nickbild/zapper_phone/transmitter_schematic/transmitter/transmitter.kicad_sch

## KiCad design transmitter_schematic/transmitter/transmitter.kicad_sch (2025-05-16)

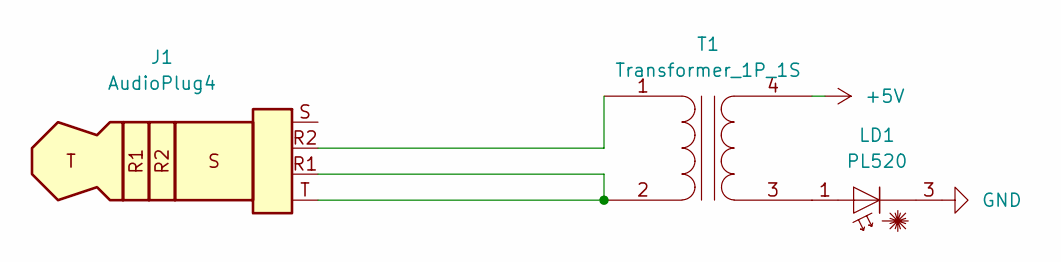
[picture p9: schematic transmitter.kicad_sch]

Parts:
J1: AudioPlug4
LD1: PL520; LaserDiode_TO38ICut-3
T1: Transformer_1P_1S

Connections:
+5V: T1.4 (SB)
GND: LD1.3 (C)
unnamed: J1.R1, J1.T, T1.2 (AB)
unnamed: J1.R2, T1.1 (AA)
unnamed: LD1.1 (A), T1.3 (SA)
